luqqqqqqq/Master-Control-Board/src/firmware/Task/Inc/user_task.h

#ifndef __USER_TASK_H
#define __USER_TASK_H

/* Includes ------------------------------------------------------------------*/
#include "stm32f4xx_hal.h"
#include "cmsis_os.h"
#include "dev_drv.h"

//user task init
void User_Task_Init(void);



#endif
